dadleyy/orient-beetle/src/beetle-srv/src/rendering/fonts.rs

use serde::{Deserialize, Serialize};
use std::io;

/// Teko @ `<https://fonts.google.com/specimen/Teko?preview.text=2:00PM&preview.text_type=custom>`
const TEKO: &[u8] = include_bytes!("../../Teko-Regular.ttf");

/// Teko @ `<https://fonts.google.com/specimen/Barlow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>`
const BARLOW: &[u8] = include_bytes!("../../Barlow-Bold.ttf");

/// DejaVu Sans @ `<https://dejavu-fonts.github.io/>`
const DEJAVU_SANS: &[u8] = include_bytes!("../../DejaVuSans.ttf");

/// Roboto Sans @ `<https://fonts.google.com/specimen/Roboto>`
const ROBOTO_SANS: &[u8] = include_bytes!("../../Roboto-Regular.ttf");

#[derive(Deserialize, Serialize, Default, Debug, Clone)]
#[serde(rename_all = "snake_case", tag = "beetle:kind", content = "beetle:content")]
/// Enumerates the fonts available to us.
pub enum FontSelection {
  /// See constant.
  Roboto,

  /// See constant.
  Teko,

  /// See constant.
  #[default]
  Barlow,

  /// See constant.
  DejaVu,
}

impl FontSelection {
  /// Returns the compile-time memory location of the font matching the selection.
  pub fn bytes(&self) -> &'static [u8] {
    match self {
      Self::Barlow => BARLOW,
      Self::DejaVu => DEJAVU_SANS,
      Self::Roboto => ROBOTO_SANS,
      Self::Teko => TEKO,
    }
  }

  /// Creates the font rendering object.
  pub fn renderer(&self) -> io::Result<rusttype::Font> {
    let font = Vec::from(self.bytes());

    rusttype::Font::try_from_vec(font).ok_or_else(|| {
      io::Error::new(
        io::ErrorKind::Other,
        "Unable to build valid font context for rasterizing",
      )
    })
  }
}
