dadleyy/orient-beetle/src/beetle-pio/include/redis_config.hpp

#ifndef _REDIS_CONFIG_H
#define _REDIS_CONFIG_H 1

#ifdef REDIS_HOST
const char * redis_host = "" REDIS_HOST;
#endif

#ifdef REDIS_PORT
const uint32_t redis_port = REDIS_PORT;
#endif

#ifdef REDIS_AUTH_USERNAME
const char * redis_auth_username = REDIS_AUTH_USERNAME;
#endif

#ifdef REDIS_AUTH_PASSWORD
const char * redis_auth_password = REDIS_AUTH_PASSWORD;
#endif

#endif
